RamazanKara/SidewinderX1_PrusaSlic3r_Profiles_-WaggsterMod/firmware/files/artillery_tft_fw_1.27.x_patch_6_/Language Packs/language_cz.ini

#### Language Code:CZ
## Language Version:20210903
## Maximum byte per keyword is 250 Bytes.
## Escape characters are not supported except newline '\n'

label_emulated_m600:Emulace M600
label_emulated_m109_m190:Emulated M109 / M190
label_rotated_ui:Otočit UI
label_language:Čeština
label_ack_notification:Styl oznámení ACK
label_files_sort_by:Řazení souborů
label_files_list_mode:Soubory jako seznam
label_fan_speed_percentage:Rychlost ventilátoru v %
label_persistent_info:Zobrazení stavových ikon
label_terminal_ack:zobrazit ACK Terminálu
label_serial_always_on:Sériový port vždy ON
label_marlin_fullscreen:Fullscreen režim Marlin
label_marlin_show_title:Zobrazit tytulek Marlin
label_marlin_type:Typ Marlin Modu
label_move_speed:Rychlost pohybu X Y Z
label_auto_load_leveling:Automaticky Leveling
label_probing_z_offset:Sondování pro Z offset
label_z_steppers_alignment:Z motor Auto-Alignment
label_ps_auto_shutdown:Auto.vypnutí
label_fil_runout:Senzor filamentu
label_pl_recovery:Obnova po ztrátě napájení
label_pl_recovery_home:Spuštění obnovení napájení
label_btt_mini_ups:Podpora BTT UPS
label_touch_sound:Zvuk při dotyku
label_toast_sound:Zvuk oznámení
label_alert_sound:Zvuk popup okna
label_heater_sound:Zvuk při dosažení teploty
label_lcd_brightness:LCD jas
label_lcd_idle_brightness:LCD snížení jasu
label_lcd_idle_time:LCD snížení jasu po
label_lcd_lock_on_idle:Blok. dotek při zatmavení
label_knob_led_color:Rotační knob LED
label_knob_led_idle:Rotační knob LED idle
label_start_gcode_enabled:Spustit Gcode před tiskem
label_end_gcode_enabled:Spustit Gcode po tisku
label_cancel_gcode_enabled:Spustit Gcode po stornu
label_steps_setting:Kroků/mm
label_filament_setting:Průměr Filamentu
label_maxacceleration:Max zrychlení
label_maxfeedrate:Max rychlost
label_acceleration:Zrychlení
label_jerk:Jerk-trhnutí
label_junction_deviation:Junction Deviation
label_home_offset:Home Offset
label_fwretract:FW Zatažení
label_fwrecover:FW Obnovení
label_retract_auto:Auto Firmware Retract
label_hotend_offset:Offset 2.trysky
label_stealth_chop:TMC Tichý režim
label_delta_configuration:Delta konfigurace
label_delta_tower_angle:Úhel věže
label_delta_endstop:Nastavení dorazu
label_probe_offset:Offset sondy
label_lin_advance:Linear Advance
label_current_setting:TMC Proud motorů(mA)
label_hybrid_threshold:TMC Hybridní práh
label_bump_sensitivity:TMC Citlivost dorazu
label_mbl_offset:MBL Offset
label_print_acceleration:Zrychlení při tisku
label_retract_acceleration:Zrychlení retrakcí
label_travel_acceleration:Zrychlení při přesunu
label_retract_length:Délka zatažení
label_retract_swap_length:Délka zatažení Swap
label_retract_feedrate:Rychlost zatažení
label_retract_z_lift:Z zvýšení při zatažení
label_recover_length:Délka obnovení
label_swap_recover_length:Délka obnovení Swap
label_recover_feedrate:Rychlost obnovení
label_swap_recover_feedrate:Rychlost obnovení Swap
label_save:Uložit
label_restore:Obnovit
label_reset:Reset
label_eeprom_save_info:Uložit nastavení tiskárny do EEPROM?
label_eeprom_restore_info:Obnovit nastavení z EEPROM?
label_eeprom_reset_info:Reset EEPROM na výchozí hodnoty?
label_settings_save:Uložení nastavení
label_settings_restore:Obnovení nastavení
label_settings_reset:Reset nastavení
label_settings_reset_info:Všechna nastavení budou obnovena na výchozí hodnoty. Pokračovat?
label_settings_reset_done:Resetování všech nastavení bylo úspěšně provedeno.\nRestartujte zařízení.
label_page_up:Další
label_page_down:Předchozí
label_up:Nahoru
label_down:Dolů
label_next:Další
label_back:Zpět
label_inc:Přidat
label_dec:Ubrat
label_load:Zavést
label_unload:Vysunout
label_on:ON
label_off:OFF
label_auto:AUTO
label_smart:SMART
label_slow:Pomalu
label_normal:Normál
label_fast:Rychle
label_zero:Vynulovat
label_half:Poloviční
label_full:Plný
label_custom:Vlastní
label_clear:Vymaž
label_default:Výchozí
label_start:Start
label_stop:Stop
label_pause:Pauza
label_resume:Obnovit
label_init:Init
label_disconnect:Odpojit
label_shut_down:Vypnout
label_force_shut_down:Vynutit
label_emergencystop:!!STOP!!
label_preheat:Zahřát
label_preheat_both:Vše
label_cooldown:Zchladit
label_confirm:Potvrdit
label_cancel:Zrušit
label_warning:Varování
label_continue:Pokračovat
label_confirmation:Jste si jistý?
label_status:Status
label_ready:Připraven
label_busy:Zpracovávám, čekejte prosím...
label_loading:Nahrávám...
label_unconnected:Tiskárna není připojena!
label_listening:TFT in Listening Mode!
label_info:Info
label_invalid_value:Neplatná hodnota/y!
label_timeout_reached:Časový limit vypršel!
label_disconnect_info:Nyní můžete tiskárnu ovládat z počítače!
label_shutting_down:Vypínám se...
label_wait_temp_shut_down:Čekám na zchladnutí trysky pod %d℃
label_power_failed:Obnovit tisk?
label_process_running:Probíhá proces!
label_process_completed:Proces dokončen!
label_process_aborted:Proces přerušen!
label_tftsd:TFT SD
label_read_tftsd_error:Chyba při čtení SD karty!
label_tftsd_inserted:SD karta vložena!
label_tftsd_removed:SD karta vyjmuta!
label_u_disk:USB Disk
label_read_u_disk_error:Chyba při čtení USB disku!
label_u_disk_inserted:USB disk  vložen!
label_u_disk_removed:USB disk vyjmut!
label_onboardsd:Onboard SD
label_read_onboardsd_error:Chyba při čtení Onboard SD!
label_filament_runout:Došel filament!
label_disable_steppers:Motory
label_xy_unlock:Uvolnit XY
label_start_print:Spustit tisk:\n%s?
label_stop_print:Zastavit tisk?
label_is_pause:Během tisku nelze extrudovat,\nmám pozastavit tisk?
label_m0_pause:Pauza po příkazu M0
label_test:Test
label_deploy:Vysunout
label_stow:Zasunout
label_repeat:Přesnost
label_nozzle:Tryska
label_bed:Stolek
label_chamber:Komora
label_fan:Ofuk
label_bltouch:BLTouch
label_touchmi:TouchMi
label_1_degree:1℃
label_5_degree:5℃
label_10_degree:10℃
label_001_mm:0,01mm
label_01_mm:0,1mm
label_1_mm:1mm
label_5_mm:5mm
label_10_mm:10mm
label_100_mm:100mm
label_200_mm:200mm
label_1_percent:1%
label_5_percent:5%
label_10_percent:10%
label_percent_value:%d%%
label_5_seconds:5 sec.
label_10_seconds:10 sec.
label_30_seconds:30 sec.
label_60_seconds:1 min.
label_120_seconds:2 min.
label_300_seconds:5 min.
label_white:Bílá
label_black:Černá
label_blue:Modrá
label_red:Červená
label_green:Zelená
label_cyan:Tyrkys
label_yellow:Žlutá
label_brown:Hnědá
label_gray:Šedá
label_orange:Oranžová
label_indigo:Indigo
label_violet:Fialová
label_magenta:Purpurová
label_purple:Nachová
label_lime:Limetková
label_darkblue:Tmavá Modrá
label_darkgreen:Tmavá Červená
label_darkgray:Tmavá Šedá
label_heat:Teplota
label_move:Posunout
label_home:Domů
label_print:Tisknout
label_extrude:Filament
label_settings:Nastavení
label_screen_settings:Displej
label_ui_settings:UI
label_sound:Zvuk
label_marlin_mode_settings:MarlinMode
label_machine_settings:Tiskárna
label_parameter_settings:Parametry
label_feature_settings:Vlastnosti
label_connection_settings:Připojení
label_serial_ports:SerialPort
label_baudrate:Rychlost
label_eeprom_settings:EEPROM
label_rgb_settings:Barva LED
label_rgb_off:LED vyp.
label_terminal:Terminál
label_leveling:Srovnat
label_point_1:Bod 1
label_point_2:Bod 2
label_point_3:Bod 3
label_point_4:Bod 4
label_point_5:Bod 5
label_bed_leveling:Bed Level
label_bl_complete:Vyrovnání kompletní
label_bl_smart_fill:Chybějící body sondy byly vyplněny inteligentně.\n\nPozn: Nezapomeň uložit!
label_bl_enable:BL: on
label_bl_disable:BL: off
label_abl:Vyrovnat
label_bbl:BBL
label_ubl:UBL
label_mbl:MBL
label_mbl_settings:Ruční vyrovnání
label_abl_settings:Auto vyrovnání
label_abl_settings_bbl:Bilineární vyrovnání
label_abl_settings_ubl:UBL vyrovnání
label_abl_settings_ubl_save:Uložit do slotu
label_abl_settings_ubl_load:Nahrát ze slotu
label_abl_slot0:Slot 0
label_abl_slot1:Slot 1
label_abl_slot2:Slot 2
label_abl_slot3:Slot 3
label_abl_slot_eeprom:Zapamatuj si slot restart? (Uložit EEPROM)
label_abl_z:Z-Slábnutí
label_level_corner:L Rohů
label_p_offset:P Offset
label_h_offset:H Offset
label_distance:Od okraje
label_load_unload:Vysunout/Zavést
label_load_unload_short:Vysunout
label_touchscreen_adjust:Kalibrovat
label_more:Více
label_screen_info:Info
label_bg_color:Barva pozadí
label_font_color:Barva písma
label_percentage:Procenta
label_percentage_speed:Rychlost
label_percentage_flow:Průtok
label_babystep:BabyStep
label_x_inc:X+
label_y_inc:Y+
label_z_inc:Z+
label_x_dec:X-
label_y_dec:Y-
label_z_dec:Z-
label_x:X
label_y:Y
label_z:Z
label_adjust_title:Kalibrace dotykové obrazovky
label_adjust_info:Dotkněte se postupně všech bodů
label_adjust_ok:Kalibrace úspěšná
label_adjust_failed:Kalibrace selhala, zopakujte znovu
label_unifiedmove:Pohyb
label_unifiedheat:Teplota
label_touch_to_exit:Pro návrat se dotkněte obrazovky...
label_mainmenu:Menu
label_leveling_edge_distance:Vzdálenost nivelačních bodů\nstolku od okraje
label_tuning:Kalibrace
label_pid:PID
label_pid_title:PID autokalibrace
label_pid_start_info:PID autokalibrace bude spuštěna. Bude to chvíli trvat.\nPokračovat?
label_pid_start_info_2:PID autokalibrace probíhá!
label_pid_start_info_3:NEDOTÝKEJ se displeje dokud není dokončeno (Zelená LED svítí)!
label_tune_extruder:E-Krok
label_tune_ext_extrude_100:100mm Vysunutí
label_tune_ext_temp:Kalibrace extruderu, ohřev
label_tune_ext_mark120mm:Označ 120mm na filamentu\nStlač '%s' pokud jsi připraven.\nZměř zbývající délku po vytlačení.
label_tune_ext_heatoff:Vypnout topení?
label_tune_ext_adj_esteps:Nastavení E-Kroků
label_tune_ext_esteps_saved:Nové E-kroky uloženy!\nNezapmeň uložit do EEPROM.\nNová hodnota: %0.2f
label_tune_ext_measured:Zbývající délka:
label_tune_ext_old_estep:Původní E-kroky: %0.2f
label_tune_ext_new_estep:Nové E-kroky: %0.2f
label_notifications:Oznámení
label_mesh_editor:Mesh síť
label_mesh_tuner:Mesh nastavení
label_case_light:Osvětlení
label_load_started:Probíhá zavádění filamentu.\nNení možná další akce, dokud to nebude dokončeno.\nProsím čekejte.
label_unload_started:Probíhá vysunování filamentu.\nNení možná další akce, dokud to nebude dokončeno.\nProsím čekejte..
label_heaters_on:Topení jsou stále zapnutá.\nChcete je vypnout?
label_print_finished:     Tisk\n   dokončen
label_main_screen:Nabídka
label_previous_print_data:Info.tisku
label_print_time:Čas tisku: %02u:%02u:%02u
label_filament_length:\nDélka filamentu: %1.2fm
label_filament_weight:\nVáha  filamentu: %1.2fg
label_filament_cost:\nCena  filamentu: %1.2f
label_no_filament_stats:\nStatistika není k dispozici.
label_click_for_more:Klikni pro více.
label_ext_templow:Teplota trysky je pod minimální teplotou (%d℃).
label_heat_hotend:Zahřát trysku na %d℃?
label_desired_templow:Teplota trysky je pod požadovanou teplotou (%d℃).
label_wait_heat_up:Počkej na cílovou teplotu.
label_z_align:Z Align
label_macros:Makro
label_mesh_valid:Test sítě
label_connect_probe:Před zahájením procesu připojte sondu. Poté ji nezapomeňte odpojit.
label_disconnect_probe:Před použitím této funkce se ujistěte, že jste odpojili sondu
label_calibration:Kalibrace
