RamazanKara/SidewinderX1_PrusaSlic3r_Profiles_-WaggsterMod/firmware/files/artillery_tft_fw_1.27.x_patch_6_/Language Packs/language_es.ini

#### Language Code:ES
## Language Version:20210903
## Maximum byte per keyword is 250 Bytes.
## Escape characters are not supported except newline '\n'

label_emulated_m600:Emulated M600
label_emulated_m109_m190:Emulated M109 / M190
label_rotated_ui:Rotar
label_language:Español
label_ack_notification:ACK notification style
label_files_sort_by:Sort files by
label_files_list_mode:Files viewer List Mode
label_fan_speed_percentage:Fan Speed As Percentage
label_persistent_info:Persistent Status Info
label_terminal_ack:Show ACK in Terminal
label_serial_always_on:Serial Always ON
label_marlin_fullscreen:Marlin mode in fullscreen
label_marlin_show_title:Marlin Mode Title Support
label_marlin_type:Marlin Mode Type
label_move_speed:Move speed(X Y Z)
label_auto_load_leveling:Auto Save Load Leveling
label_probing_z_offset:Probing for Z offset
label_z_steppers_alignment:Z Steppers Auto-Alignment
label_ps_auto_shutdown:Apag. aut.
label_fil_runout:Filament sensor
label_pl_recovery:Power loss recovery
label_pl_recovery_home:Power Loss Recovery Homing
label_btt_mini_ups:BTT UPS Support
label_touch_sound:Touch sounds
label_toast_sound:Toast Notifications
label_alert_sound:Popups and Alerts
label_heater_sound:Heater notification
label_lcd_brightness:Brightness
label_lcd_idle_brightness:Idle brightness
label_lcd_idle_time:Idle timeout
label_lcd_lock_on_idle:LCD lock on idle
label_knob_led_color:Rotary Knob LED
label_knob_led_idle:Rotary Knob LED idle
label_start_gcode_enabled:Start Gcode before print
label_end_gcode_enabled:End Gcode after print
label_cancel_gcode_enabled:Cancel Gcode
label_steps_setting:Steps per mm
label_filament_setting:Filament Diameter
label_maxacceleration:Max Acceleration
label_maxfeedrate:Max Feed Rate
label_acceleration:Acceleration
label_jerk:Jerk
label_junction_deviation:Junction Deviation
label_home_offset:Home Offset
label_fwretract:FW Retraction
label_fwrecover:FW Retraction Recover
label_retract_auto:Auto Firmware Retract
label_hotend_offset:Offset 2nd Nozzle
label_stealth_chop:TMC StealthChop
label_delta_configuration:Delta Configuration
label_delta_tower_angle:Tower Angle Trim
label_delta_endstop:Endstop Adjustments
label_probe_offset:Sonda Compensar
label_lin_advance:Linear Advance
label_current_setting:Driver Current (mA)
label_hybrid_threshold:TMC HybridThreshold
label_bump_sensitivity:TMC bump sensitivity
label_mbl_offset:MBL Offset
label_print_acceleration:Print Acceleration
label_retract_acceleration:Retract Acceleration
label_travel_acceleration:Travel Acceleration
label_retract_length:Retract length
label_retract_swap_length:Retract swap length
label_retract_feedrate:Retract feedrate
label_retract_z_lift:Z lift on retraction
label_recover_length:Extra recover length
label_swap_recover_length:Extra recover swap length
label_recover_feedrate:Recover feedrate
label_swap_recover_feedrate:Swap recover feedrate
label_save:Grabar
label_restore:Restore
label_reset:Reset
label_eeprom_save_info:Save printer settings to EEPROM?
label_eeprom_restore_info:Reload settings from EEPROM?
label_eeprom_reset_info:Reset EEPROM to stock printer settings?
label_settings_save:Save settings
label_settings_restore:Restore settings
label_settings_reset:Reset default settings
label_settings_reset_info:Reset all settings to default values?
label_settings_reset_done:Reset all settings successful.\nplease restart the device.
label_page_up:Retroceder
label_page_down:Avanzar
label_up:Up
label_down:Down
label_next:Next
label_back:Volver
label_inc:Aumentar
label_dec:Disminur
label_load:Cargar
label_unload:Descargar
label_on:ON
label_off:OFF
label_auto:AUTO
label_smart:SMART
label_slow:Despacio
label_normal:Normal
label_fast:Rápido
label_zero:Cero
label_half:Mitad
label_full:Todo
label_custom:Personalizar
label_clear:Clear
label_default:Default
label_start:Start
label_stop:Parar
label_pause:Pausar
label_resume:Continuar
label_init:Init
label_disconnect:Desconectar
label_shut_down:Apagar
label_force_shut_down:Forzar Apagado
label_emergencystop:PARADA EMERGENCIA
label_preheat:Precalentar
label_preheat_both:Ambos
label_cooldown:Enfriarse
label_confirm:Confirmar
label_cancel:Cancelar
label_warning:Advertencia
label_continue:Continuar
label_confirmation:Are you sure?
label_status:Status
label_ready:Preparado
label_busy:Procesamiento ocupado, por favor espere...
label_loading:Cargando...
label_unconnected:¡No hay comunicación con impresora!
label_listening:TFT in Listening Mode!
label_info:Info
label_invalid_value:Invalid value(s)
label_timeout_reached:Timeout reached!
label_disconnect_info:¡Ahora puede controlar la impresora desde su ordenador!
label_shutting_down:Apagando...
label_wait_temp_shut_down:Espere a que la temperatura del hotend sea inferior a %d℃
label_power_failed:¿Continuar imprimiendo?
label_process_running:Process already running!
label_process_completed:Process completed!
label_process_aborted:Process aborted!
label_tftsd:SD TFT
label_read_tftsd_error:¡Error en la tarjeta SD TFT!
label_tftsd_inserted:¡Tarjeta insertada!
label_tftsd_removed:¡Tarjeta extraida!
label_u_disk:Pendrive
label_read_u_disk_error:¡Error en el Pendrive!
label_u_disk_inserted:¡Pendrive insertado!
label_u_disk_removed:¡Pendrive extraido!
label_onboardsd:SD Placa
label_read_onboardsd_error:¡Error en la tarjeta SD de la placa!
label_filament_runout:¡Filamento agotado!
label_disable_steppers:Disarm All
label_xy_unlock:Desbloquear XY
label_start_print:Start Printing:\n%s?
label_stop_print:¿Desea parar la impresión?
label_is_pause:No se puede extruir al imprimir,¿\nPausar la impresión?
label_m0_pause:Paused by M0 command
label_test:Probar
label_deploy:Desplegar
label_stow:Plegar
label_repeat:Repetir
label_nozzle:Punta
label_bed:Cama
label_chamber:Chamber
label_fan:Ventilar
label_bltouch:BLTouch
label_touchmi:TouchMi
label_1_degree:1℃
label_5_degree:5℃
label_10_degree:10℃
label_001_mm:0.01mm
label_01_mm:0.1mm
label_1_mm:1mm
label_5_mm:5mm
label_10_mm:10mm
label_100_mm:100mm
label_200_mm:200mm
label_1_percent:1%
label_5_percent:5%
label_10_percent:10%
label_percent_value:%d%%
label_5_seconds:5 Sec.
label_10_seconds:10 Sec.
label_30_seconds:30 Sec.
label_60_seconds:1 Min.
label_120_seconds:2 Min.
label_300_seconds:5 Min.
label_white:Blanco
label_black:Negro
label_blue:Azul
label_red:Rojo
label_green:Verde
label_cyan:Cyan
label_yellow:Amarillo
label_brown:Marrón
label_gray:Gris
label_orange:Orange
label_indigo:Indigo
label_violet:Violet
label_magenta:Magenta
label_purple:Purple
label_lime:Lime
label_darkblue:DarkBlue
label_darkgreen:DarkGreen
label_darkgray:DarkGray
label_heat:Calentar
label_move:Mover
label_home:Origen
label_print:Imprimir
label_extrude:Extruir
label_settings:Configurar
label_screen_settings:Pantalla
label_ui_settings:UI
label_sound:Sound
label_marlin_mode_settings:MarlinMode
label_machine_settings:Máquina
label_parameter_settings:Parámetro
label_feature_settings:Añadidos
label_connection_settings:Connection
label_serial_ports:S. Ports
label_baudrate:BaudRate
label_eeprom_settings:EEPROM
label_rgb_settings:Color LED
label_rgb_off:Apagar LED
label_terminal:Terminal
label_leveling:Nivelar
label_point_1:Punto 1
label_point_2:Punto 2
label_point_3:Punto 3
label_point_4:Punto 4
label_point_5:Punto 5
label_bed_leveling:Bed Level
label_bl_complete:Bed Leveling Complete
label_bl_smart_fill:Missing probe points have been smart filled.\n\nNote: remember to save!
label_bl_enable:BL: on
label_bl_disable:BL: off
label_abl:ABL
label_bbl:BBL
label_ubl:UBL
label_mbl:MBL
label_mbl_settings:Mesh Bed Leveling
label_abl_settings:Auto Bed Leveling
label_abl_settings_bbl:Bilinear Bed Leveling
label_abl_settings_ubl:Unified Bed Leveling
label_abl_settings_ubl_save:Save to slot
label_abl_settings_ubl_load:Load from slot
label_abl_slot0:Slot 0
label_abl_slot1:Slot 1
label_abl_slot2:Slot 2
label_abl_slot3:Slot 3
label_abl_slot_eeprom:Save the mesh to EEPROM to load after reboot?
label_abl_z:Z Fade
label_level_corner:L corner
label_p_offset:P Offset
label_h_offset:H Offset
label_distance:Distance
label_load_unload:Load/Unload
label_load_unload_short:(Un)Load
label_touchscreen_adjust:Calibrar
label_more:Más
label_screen_info:Informar
label_bg_color:Background color
label_font_color:Font color
label_percentage:Porcentaje
label_percentage_speed:Velocidad
label_percentage_flow:Flujo
label_babystep:BabyStep
label_x_inc:+X
label_y_inc:+Y
label_z_inc:+Z
label_x_dec:-X
label_y_dec:-Y
label_z_dec:-Z
label_x:X
label_y:Y
label_z:Z
label_adjust_title:¡Calibrar la pantalla táctil
label_adjust_info:Por favor haga clic en el punto rojo
label_adjust_ok:Ajuste correcto
label_adjust_failed:Ajuste fallido, por favor intentelo de nuevo
label_unifiedmove:Movimiento
label_unifiedheat:Calor/Ventilador
label_touch_to_exit:Toca cualquier lugar para salir
label_mainmenu:Menu
label_leveling_edge_distance:Bed edge distance
label_tuning:Tuning
label_pid:PID
label_pid_title:PID autotune
label_pid_start_info:PID autotune may take some time to complete.\nContinue?
label_pid_start_info_2:PID autotune in progress!
label_pid_start_info_3:Do not touch the screen until completed (green LED ON)!
label_tune_extruder:Tune steps
label_tune_ext_extrude_100:Ext. 100mm
label_tune_ext_temp:Extruder tuning | Heat
label_tune_ext_mark120mm:Mark 120 mm on your fillament.\nPress '%s' when ready.\nMeasure remaining length after extruding.
label_tune_ext_heatoff:Turn the heater off?
label_tune_ext_adj_esteps:Adjust E-Steps
label_tune_ext_esteps_saved:New E-steps applied.\nDon't forget to save it in EEPROM.\nNew value: %0.2f
label_tune_ext_measured:Length remaining:
label_tune_ext_old_estep:Old e-steps: %0.2f
label_tune_ext_new_estep:New e-steps: %0.2f
label_notifications:Notifications
label_mesh_editor:Mesh edit
label_mesh_tuner:Mesh tuner
label_case_light:Case light
label_load_started:Loading filament.\nPlease wait for the process to complete.
label_unload_started:Unloading filament.\nPlease wait for the process to complete.
label_heaters_on:Some heaters are still ON.\nDo you want to stop them?
label_print_finished:   Print\n   finished
label_main_screen:Main
label_previous_print_data:Brief
label_print_time:Print Time: %02u:%02u:%02u
label_filament_length:\nFilament length: %1.2fm
label_filament_weight:\nFilament weight: %1.2fg
label_filament_cost:\nFilament cost: %1.2f
label_no_filament_stats:\nFilament data not available.
label_click_for_more:Click for summary
label_ext_templow:Hotend temperature is below minimum temperature (%d℃).
label_heat_hotend:Heat hotend to %d℃?
label_desired_templow:Hotend temperature is below\ndesired temperature (%d℃).
label_wait_heat_up:Wait for it to heat up.
label_z_align:Z Align
label_macros:Macros
label_mesh_valid:Mesh Validation
label_connect_probe:Connect probe before starting the process. Make sure to disconnect it afterwards.
label_disconnect_probe:Make sure you have disconnected probe before using this feature.
label_calibration:Calibration
